weteor/ChonkyKong/pcb/chonky.kicad_sch

## KiCad design pcb/chonky.kicad_sch (2023-04-05)

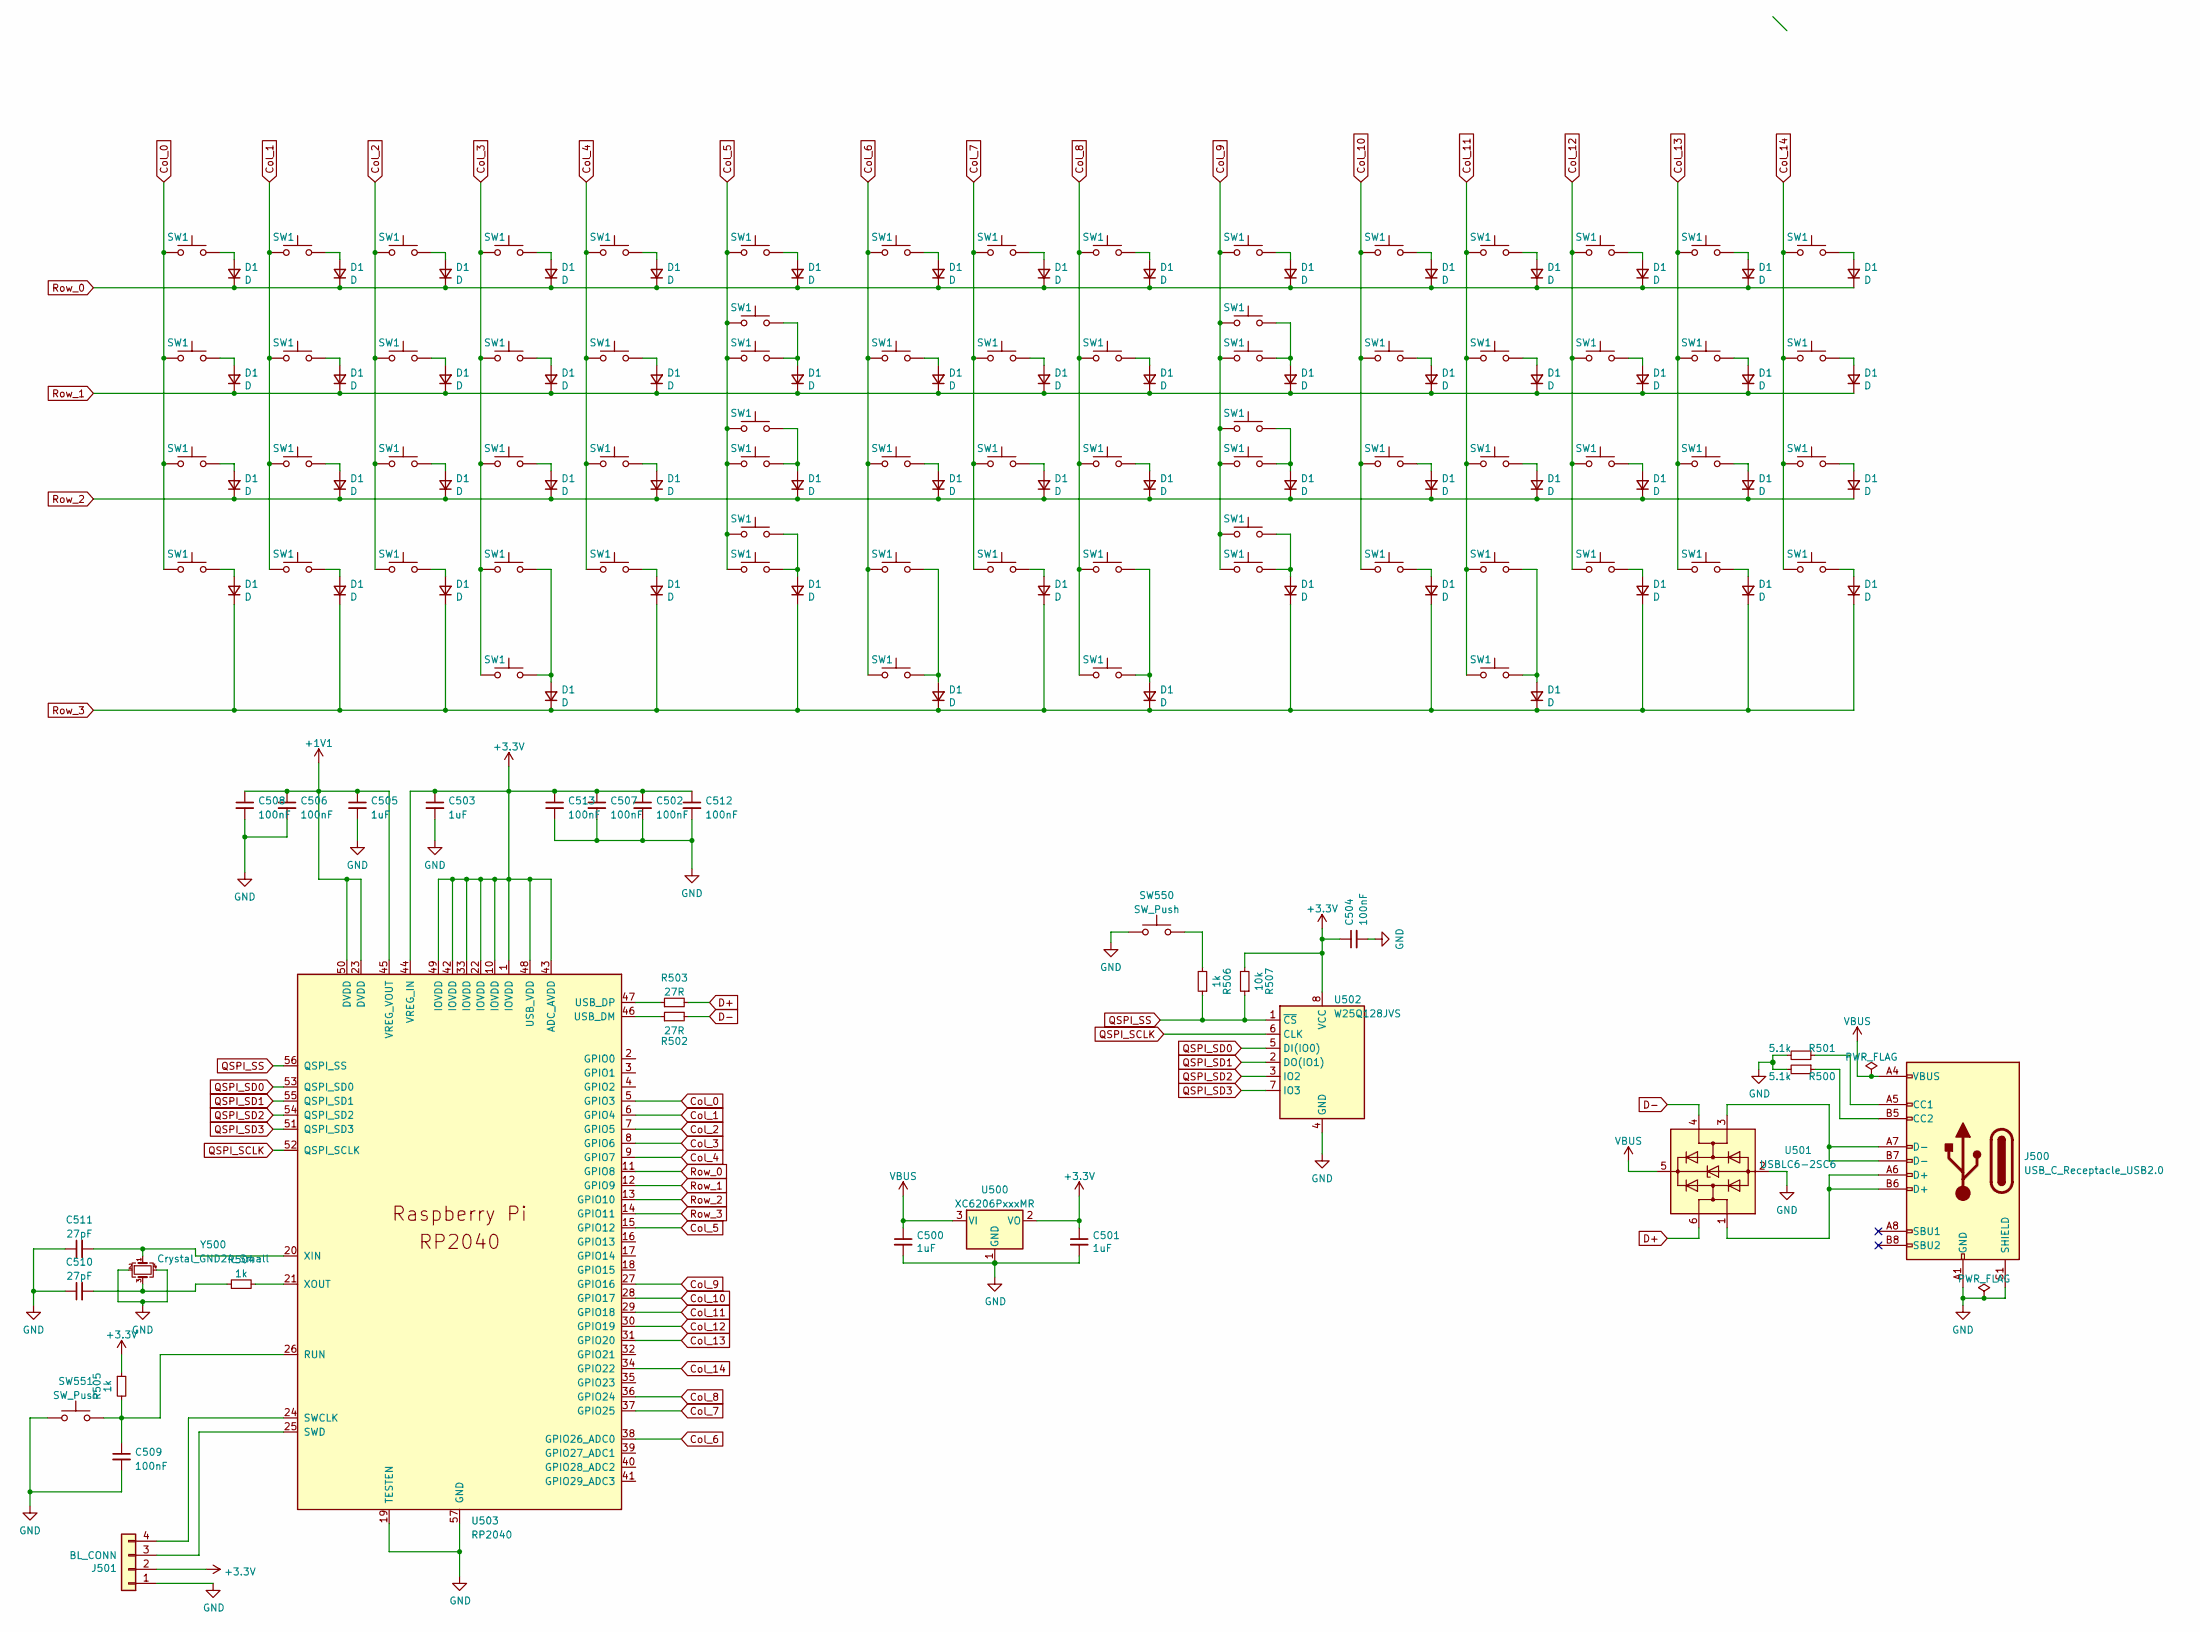
[picture p4: schematic chonky.kicad_sch]

Parts:
C500, C501, C503, C505: 1uF; C_0402_1005Metric
C502, C504, C506, C507, C508, C509, C512, C513: 100nF; C_0402_1005Metric
C510, C511: 27pF; C_0402_1005Metric
D1: D; D_SOD-123
J500: USB_C_Receptacle_USB2.0; USB C-31-M-12
J501: BL_CONN; PinHeader_1x04_P2.54mm_Vertical
R500, R501: 5.1k; R_0402_1005Metric
R502, R503: 27R; R_0402_1005Metric
R504, R505, R506: 1k; R_0402_1005Metric
R507: 10k; R_0402_1005Metric
SW1: SW_Push; CherryMX_Hotswap
SW550, SW551: SW_Push; Micro_Push_Button_3x6x2.5mm
U500: XC6206PxxxMR; SOT-23-3
U501: USBLC6-2SC6; SOT-23-6
U502: W25Q128JVS; SOIC-8_5.23x5.23mm_P1.27mm
U503: RP2040; RP2040-QFN-56
Y500: Crystal_GND24_Small; Crystal_SMD_2520-4Pin_2.5x2.0mm

Connections:
+1V1: C505.1, C506.1, C508.1, U503.23 (DVDD), U503.45 (VREG_VOUT), U503.50 (DVDD)
+3.3V: C501.1, C502.1, C503.1, C504.1, C507.1, C512.1, C513.1, J501.2, R505.1, R507.2, U500.2 (VO), U502.8 (VCC), U503.1 (IOVDD), U503.10 (IOVDD), U503.22 (IOVDD), U503.33 (IOVDD), U503.42 (IOVDD), U503.43 (ADC_AVDD), U503.44 (VREG_IN), U503.48 (USB_VDD), U503.49 (IOVDD)
Col_0: SW1.1, U503.5 (GPIO3)
Col_1: SW1.1, U503.6 (GPIO4)
Col_2: SW1.1, U503.7 (GPIO5)
Col_3: SW1.1, U503.8 (GPIO6)
Col_4: SW1.1, U503.9 (GPIO7)
Col_5: SW1.1, U503.15 (GPIO12)
Col_6: SW1.1, U503.38 (GPIO26_ADC0)
Col_7: SW1.1, U503.37 (GPIO25)
Col_8: SW1.1, U503.36 (GPIO24)
Col_9: SW1.1, U503.27 (GPIO16)
Col_10: SW1.1, U503.28 (GPIO17)
Col_11: SW1.1, U503.29 (GPIO18)
Col_12: SW1.1, U503.30 (GPIO19)
Col_13: SW1.1, U503.31 (GPIO20)
Col_14: SW1.1, U503.34 (GPIO22)
D+: R503.2, U501.6 (I/O1)
D-: R502.2, U501.4 (I/O2)
GND: C500.2, C501.2, C502.2, C503.2, C504.2, C505.2, C506.2, C507.2, C508.2, C509.2, C510.1, C511.1, C512.2, C513.2, J500.A1 (GND), J500.A12 (GND), J500.B1 (GND), J500.B12 (GND), J500.S1 (SHIELD), J501.1, R500.2, R501.2, SW550.1, SW551.1, U500.1 (GND), U501.2 (GND), U502.4 (GND), U503.19 (TESTEN), U503.57 (GND), Y500.2, Y500.4
unnamed: C509.1, R505.2, SW551.2, U503.26 (RUN)
unnamed: C510.2, R504.1, Y500.3
unnamed: C511.2, U503.20 (XIN), Y500.1
unnamed: D1.2 (A), SW1.2
unnamed: J500.A5 (CC1), R501.1
unnamed: J500.A6 (D+), J500.B6 (D+), U501.1 (I/O1)
unnamed: J500.A7 (D-), J500.B7 (D-), U501.3 (I/O2)
unnamed: J500.B5 (CC2), R500.1
unnamed: J501.3, U503.25 (SWD)
unnamed: J501.4, U503.24 (SWCLK)
unnamed: R502.1, U503.46 (USB_DM)
unnamed: R503.1, U503.47 (USB_DP)
unnamed: R504.2, U503.21 (XOUT)
unnamed: R506.2, SW550.2
QSPI_SCLK: U502.6 (CLK), U503.52 (QSPI_SCLK)
QSPI_SD0: U502.5 (DI(IO0)), U503.53 (QSPI_SD0)
QSPI_SD1: U502.2 (DO(IO1)), U503.55 (QSPI_SD1)
QSPI_SD2: U502.3 (IO2), U503.54 (QSPI_SD2)
QSPI_SD3: U502.7 (IO3), U503.51 (QSPI_SD3)
QSPI_SS: R506.1, R507.1, U502.1 (~CS), U503.56 (QSPI_SS)
Row_0: D1.1 (K), U503.11 (GPIO8)
Row_1: D1.1 (K), U503.12 (GPIO9)
Row_2: D1.1 (K), U503.13 (GPIO10)
Row_3: D1.1 (K), U503.14 (GPIO11)
VBUS: C500.1, J500.A4 (VBUS), J500.A9 (VBUS), J500.B4 (VBUS), J500.B9 (VBUS), U500.3 (VI), U501.5 (VBUS)
